adityamahes/6DOFRoboticArm/TeslaOptimusCAD/Hingea.STL

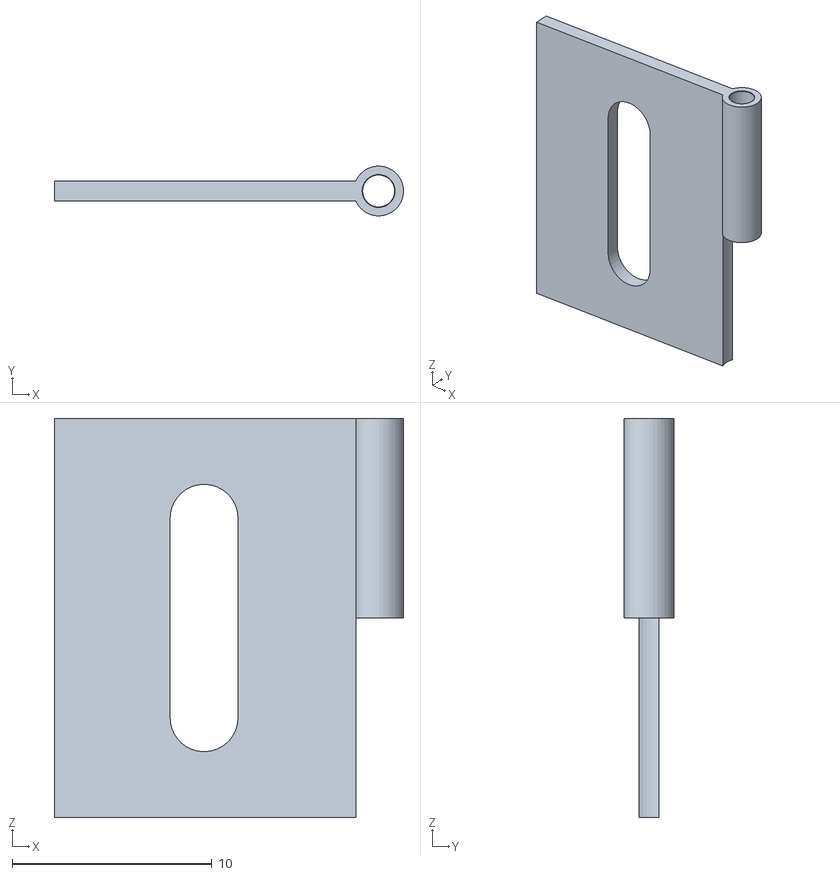
[picture p15: CAD file, 2026-01-31]
TeslaOptimusCAD/Hingea.STL
17.5 x 2.50 x 20.0
