adityamahes/6DOFRoboticArm/Optimus Body/Base Cover Optimus v2.SLDPRT

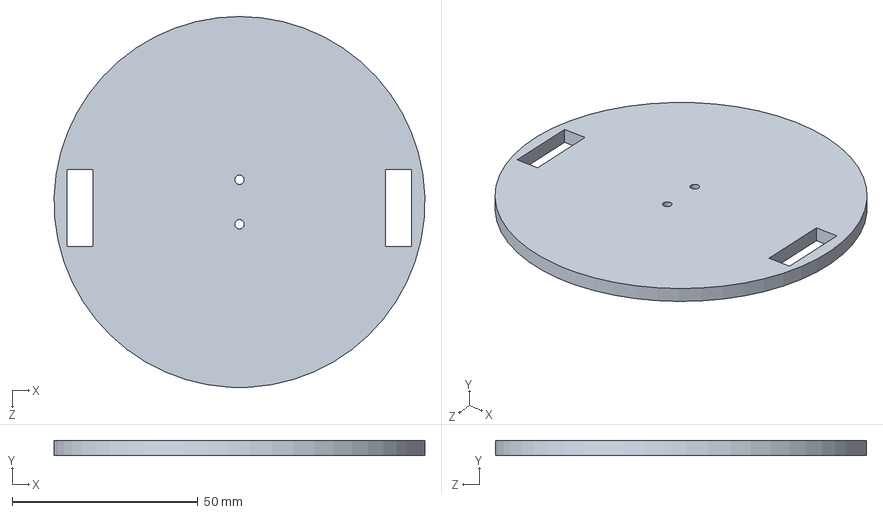
[picture p16: CAD file, 2026-02-03]
Optimus Body/Base Cover Optimus v2.SLDPRT
100.0 x 4.00 x 100.0 mm
