adityamahes/6DOFRoboticArm/Optimus Body/optimus base.SLDPRT

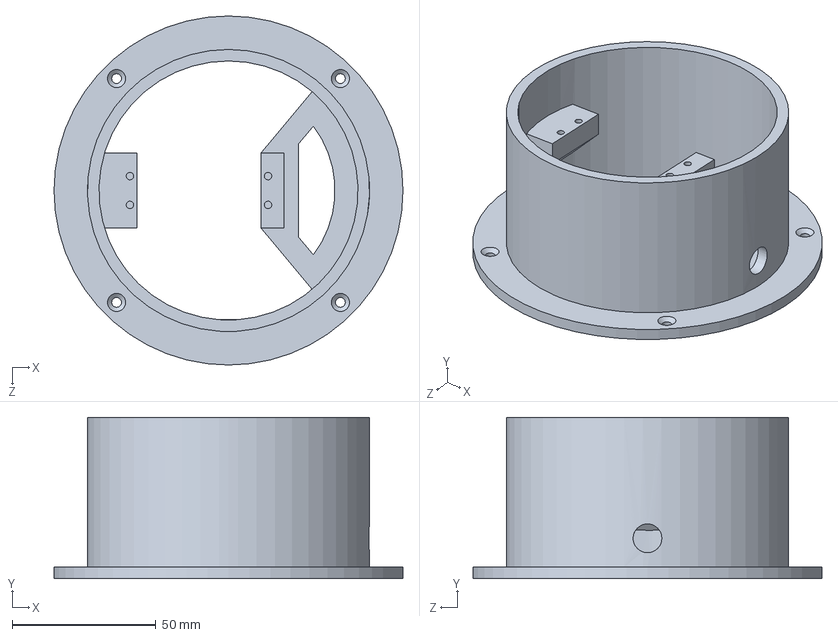
[picture p17: CAD file, 2026-02-03]
Optimus Body/optimus base.SLDPRT
121.2 x 56.0 x 121.2 mm
