adityamahes/6DOFRoboticArm/Optimus Body/Optimus Arm #2 V2.SLDPRT

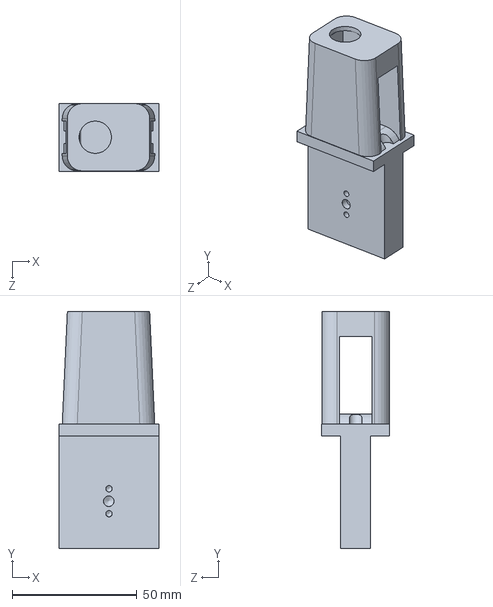
[picture p18: CAD file, 2026-02-03]
Optimus Body/Optimus Arm #2 V2.SLDPRT
40.0 x 95.0 x 27.2 mm
